LIV2/CIDER/RTL/top.v

`timescale 1ns / 1ps
/*
 * Copyright (C) 2023 Matthew Harlum <matt@harlum.net>
 *
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
 * You should have received a copy of the GNU General Public License
 * along with this program; if not, write to the Free Software Foundation,
 * Inc., 51 Franklin Street, Fifth Floor, Boston, MA 02110-1301, USA.
 */
module CIDER(
    inout [15:12] DBUS,
    input [23:1] ADDR,
    input BERR_n,
    input UDS_n,
    input LDS_n,
    input RW,
    inout AS_n,
    input RESET_n,
    input ECLK,
    output DTACK_n,
    output OVR_1_n,
    output OVR_2_n,
    input  A500_n,
    output EXTEN_n,
// IDE stuff
    input IDEEN_n,
    input IORDY,
    output IOR_n,
    output IOW_n,
    output IDECS1_n,
    output IDECS2_n,
    output IDEBUF_OE,
    output IDE_ROMEN,
// SDRAM Stuff
    input MEMCLK,
    input RAM_EN_n,
    input RANGER_EN_n,
    output MEMW_n,
    output RAS_n,
    output CAS_n,
    output CKE,
    output DQML,
    output DQMH,
    output RAMCS_n,
    output [11:0] MA,
    output [1:0] BA,
    output RAMOE_n,
// FLASH Stuff
    input FLASH_BANK_SEL_n,
    input FLASH_EN_n,
    output FLASH_CE_n,
    output FLASH_A18,
    output FLASH_A19
    );

`include "globalparams.vh"

wire autoconfig_cycle;
wire ctrl_access;
wire flash_access;
wire [3:0] autoconfig_dout;
wire [3:0] ctrl_dout;
wire ram_dtack;
wire autoconf_dtack;

reg ranger_enabled;
reg flash_enabled;
reg flash_bank;
reg ext_en;

assign EXTEN_n = flash_enabled || ~ext_en;

wire ram_access;
wire ide_access;

wire otherram_enabled;

always @(posedge MEMCLK) begin
  if (!RESET_n) begin
    ext_en         <= A500_n;
    flash_bank     <= ~FLASH_BANK_SEL_n;
    flash_enabled  <= ~FLASH_EN_n;
    ranger_enabled <= ~RANGER_EN_n;
  end
end

reg [1:0] UDS_n_sync;
reg [1:0] LDS_n_sync;
reg [2:0] AS_n_sync;
reg [1:0] RW_sync;

always @(posedge MEMCLK or negedge RESET_n) begin
  if (!RESET_n) begin
    UDS_n_sync <= 2'b11;
    LDS_n_sync <= 2'b11;
    AS_n_sync  <= 3'b111;
    RW_sync    <= 2'b11;
  end else begin
    UDS_n_sync[1:0] <= {UDS_n_sync[0],UDS_n};
    LDS_n_sync[1:0] <= {LDS_n_sync[0],LDS_n};
    AS_n_sync[2:0]  <= {AS_n_sync[1:0],AS_n};
    RW_sync         <= {RW_sync[0],RW};
  end
end

reg [1:0] z2_state;
reg dtack;

always @(posedge MEMCLK or negedge RESET_n) begin
  if (!RESET_n) begin
    z2_state <= Z2_IDLE;
    dtack <= 0;
  end else begin
    if (AS_n_sync[1] == 1) begin
      dtack <= 0;
    end else if (ram_dtack) begin
      dtack <= 1;
    end

    case (z2_state)
      Z2_IDLE:
        begin
          if (~AS_n_sync[1] && (ctrl_access || ram_access || autoconfig_cycle)) begin
            z2_state <= Z2_START;
          end
        end
      Z2_START:
        begin
          if (!UDS_n_sync[1] || !LDS_n_sync[1]) begin
            z2_state <= Z2_DATA;
          end
        end
      Z2_DATA:
        begin
          if (ctrl_access || ram_dtack || autoconf_dtack) begin
            z2_state <= Z2_END;
          end
        end
      Z2_END:
        if (AS_n_sync[1]) begin
          z2_state <= Z2_IDLE;
        end
    endcase
  end
end

Autoconfig AUTOCONFIG (
  .ADDR (ADDR),
  .AS_n (AS_n_sync[1]),
  .RW (RW_sync[1]),
  .CLK (MEMCLK),
  .DIN (DBUS[15:12]),
  .RESET_n (RESET_n),
  .ram_access (ram_access),
  .RAM_EN (~RAM_EN_n),
  .RANGER_EN (ranger_enabled),
  .OTHER_EN (otherram_enabled),
`ifndef PROTO_A
  .ext_en (ext_en),
`else
  .ext_en (1'b1),
`endif
  .mapram_en (mapram_en),
  .ide_enabled (~IDEEN_n),
  .autoconfig_cycle (autoconfig_cycle),
  .DOUT (autoconfig_dout),
  .z2_state (z2_state),
  .dtack (autoconf_dtack),
  .maprom_en (flash_enabled),
  .ctrl_access (ctrl_access),
  .ide_access (ide_access),
  .flash_access (flash_access),
  .OVL (OVL)
);

SDRAM SDRAM (
  .ADDR (ADDR[23:1]),
  .z2_state (z2_state),
  .UDS_n (UDS_n_sync[1]),
  .LDS_n (LDS_n_sync[1]),
  .RAM_CYCLE (ram_access),
  .RESET_n (RESET_n),
  .RW (RW_sync[1]),
  .CLK (MEMCLK),
  .CKE (CKE),
  .BA (BA),
  .MADDR (MA),
  .CAS_n (CAS_n),
  .RAS_n (RAS_n),
  .CS_n (RAMCS_n),
  .WE_n (MEMW_n),
  .DQML (DQML),
  .DQMH (DQMH),
  .dtack (ram_dtack),
  .ECLK (ECLK)
);

IDE IDE (
  .ADDR (ADDR[23:12]),
  .RW (RW),
  .AS_n (AS_n_sync[1]),
  .CLK (MEMCLK),
  .IORDY (IORDY),
  .IDECS1_n (IDECS1_n),
  .IDECS2_n (IDECS2_n),
  .ide_access (ide_access),
  .ide_enable (~IDEEN_n),
  .RESET_n (RESET_n),
  .IDEBUF_OE (IDEBUF_OE),
  .IDE_ROMEN (IDE_ROMEN)
);

ControlReg ControlReg (
  .ADDR (ADDR[23:16]),
  .DIN (DBUS[15:12]),
  .DOUT (ctrl_dout),
  .CLK (MEMCLK),
  .ctrl_access (ctrl_access),
  .RW (RW_sync[1]),
  .AS_n (AS_n_sync[1]),
  .z2_state (z2_state),
  .RESET_n (RESET_n),
  .otherram_en (otherram_enabled),
  .flash_enabled (flash_enabled),
  .flash_a18  (FLASH_A18),
  .flash_a19  (FLASH_A19),
  .flash_bank (flash_bank),
  .OVL (OVL),
  .mapram_en (mapram_en)
);

wire ds = !UDS_n || !LDS_n;

reg [2:0] ds_delay;

always @(posedge MEMCLK or negedge ds)
begin
  if (!ds) begin
    ds_delay <= 'b0;
  end else begin
    if (ds_delay < 3'd7) begin
      ds_delay <= ds_delay + 1;
    end
  end
end


// IOR assertion delayed by ~100ns after AS_n to meet t1 Address Setup time for IOR
// IOW asserted in S4, deasserted ~120ns later so that t4 IOW data hold time is met
assign IOR_n = !(RW && !AS_n && ds && ds_delay > 3'd5);
assign IOW_n = !(!RW && !AS_n && ds && ds_delay < 3'd6);

assign DBUS[15:12] = (autoconfig_cycle || ctrl_access) && RW && !UDS_n && RESET_n ? (autoconfig_cycle) ? autoconfig_dout : ctrl_dout[3:0] : 'bZ;

assign RAMOE_n = !(ram_access && !AS_n && RESET_n);

assign FLASH_CE_n = ~flash_access || AS_n;

wire OVR = (ram_access || ide_access || flash_access) ? 1'b0 : 1'bZ;

assign OVR_1_n = OVR;
assign OVR_2_n = OVR;

assign DTACK_n = (((ram_access && dtack) || ide_access || flash_access) && !AS_n) ? 1'b0 : 1'bZ;

endmodule
